sctanf/picoamp-PCB/images/DSC_0401.webp

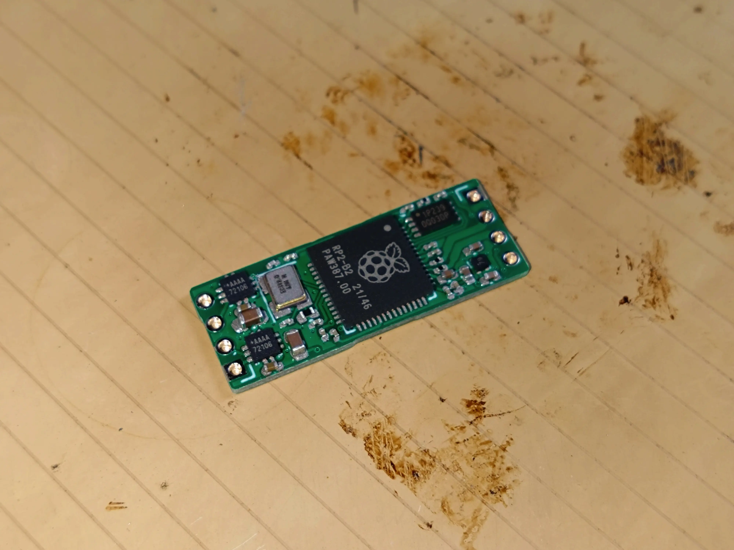
images/DSC_0401.webp
