sctanf/picoamp-PCB/images/DSC_0409.webp

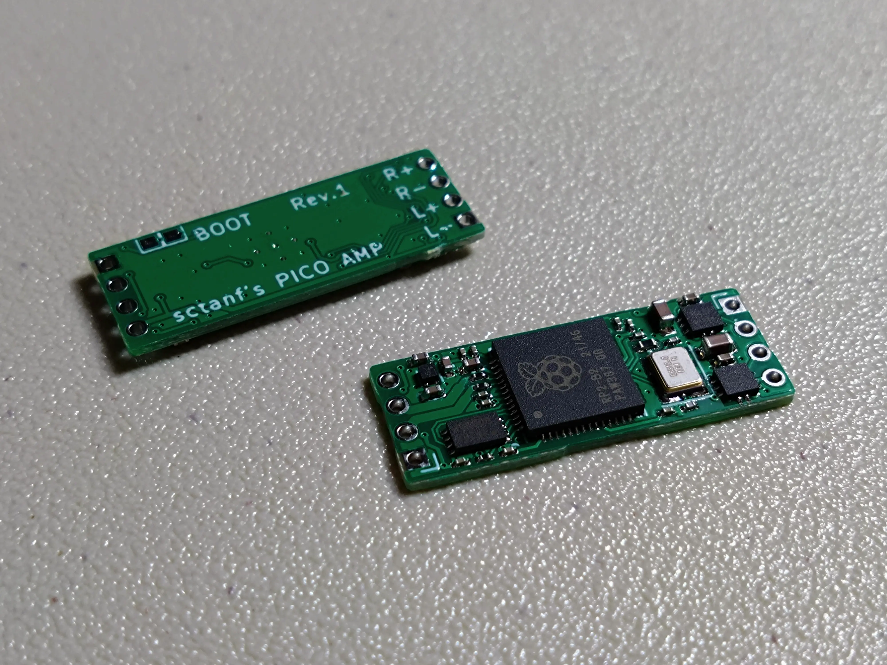
images/DSC_0409.webp
